hazimeyou/YMMKeyboard/firmware/src/RP2040TinyUsb/src/tusb_config.h

#pragma once

#ifdef __cplusplus
extern "C" {
#endif

#define CFG_TUSB_MCU                 OPT_MCU_RP2040
#define CFG_TUSB_RHPORT0_MODE        (OPT_MODE_DEVICE)
#define CFG_TUSB_OS                  OPT_OS_PICO

#ifndef CFG_TUSB_DEBUG
#define CFG_TUSB_DEBUG               0
#endif

#define CFG_TUD_ENDPOINT0_SIZE       64

#define CFG_TUD_CDC                  1
#define CFG_TUD_HID                  1
#define CFG_TUD_MSC                  0
#define CFG_TUD_MIDI                 0
#define CFG_TUD_VENDOR               0

#define CFG_TUD_CDC_RX_BUFSIZE       256
#define CFG_TUD_CDC_TX_BUFSIZE       256
#define CFG_TUD_CDC_EP_BUFSIZE       64

#define CFG_TUD_HID_EP_BUFSIZE       64

#ifdef __cplusplus
}
#endif
